agarnung/miniVirgil/assets/enviando.png

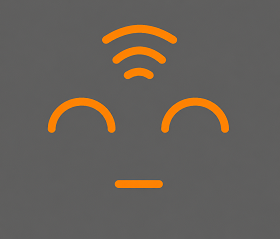
assets/enviando.png
