agarnung/miniVirgil/assets/espera.png

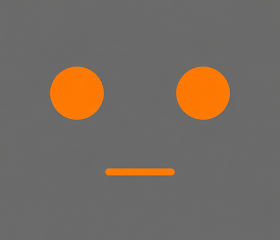
assets/espera.png
