agarnung/miniVirgil/assets/grabando.png

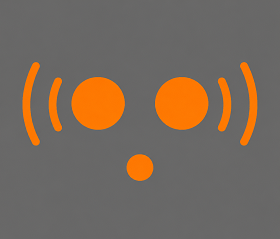
assets/grabando.png
