agarnung/miniVirgil/assets/iniciando.png

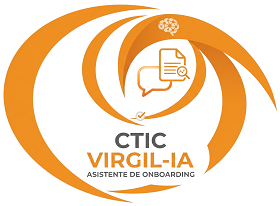
assets/iniciando.png
