agarnung/miniVirgil/assets/proceso.png

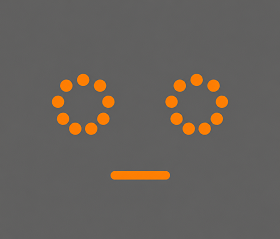
assets/proceso.png
